rsfis/RIAN-MICROCOMPUTER/cart/aliexpress.png

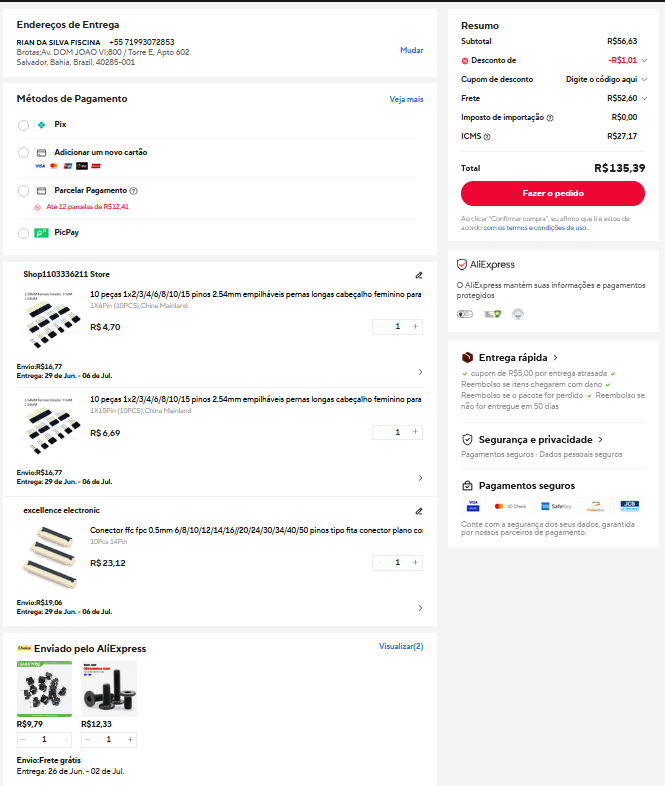
cart/aliexpress.png
