rsfis/RIAN-MICROCOMPUTER/cart/jlc.png

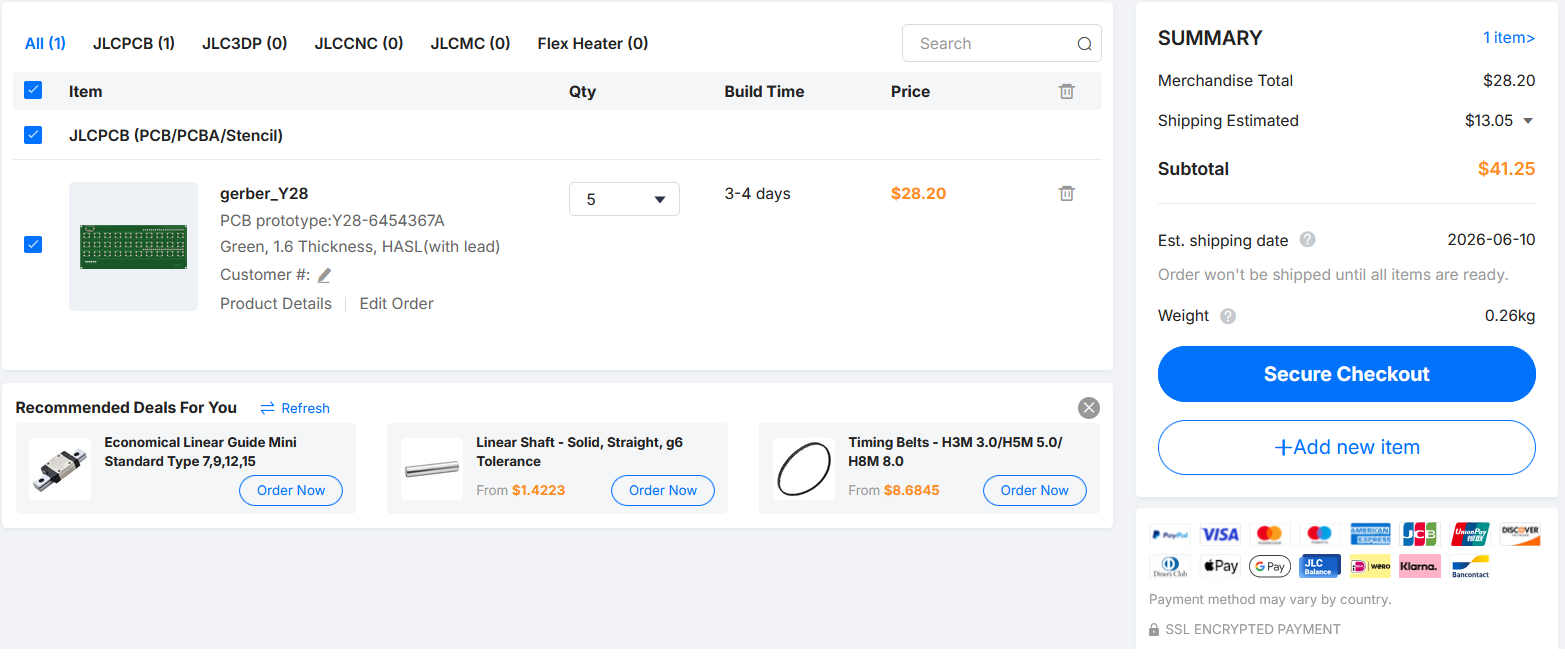
cart/jlc.png
