rsfis/RIAN-MICROCOMPUTER/firmware/!draft/colours.png

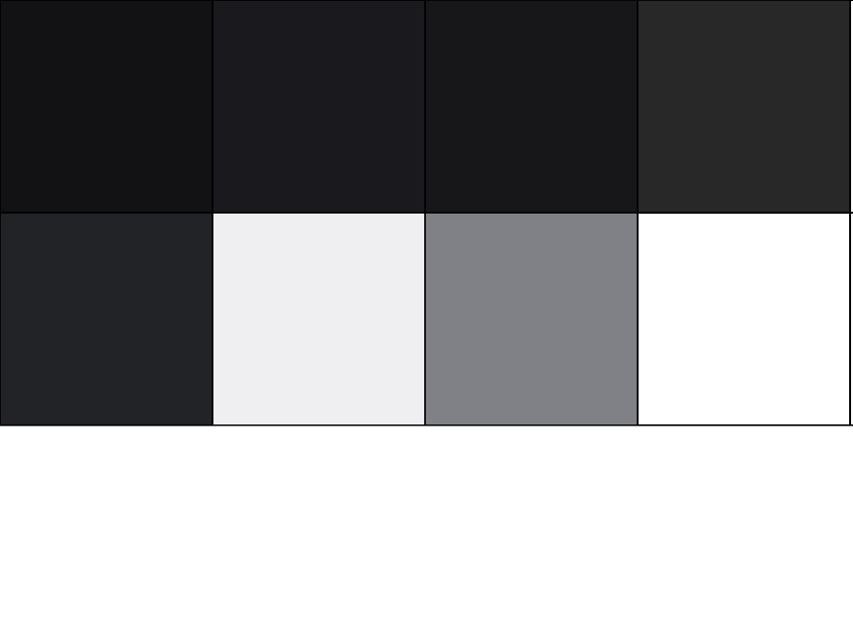
firmware/!draft/colours.png
