rsfis/RIAN-MICROCOMPUTER/firmware/!draft/export/desktop_page.png

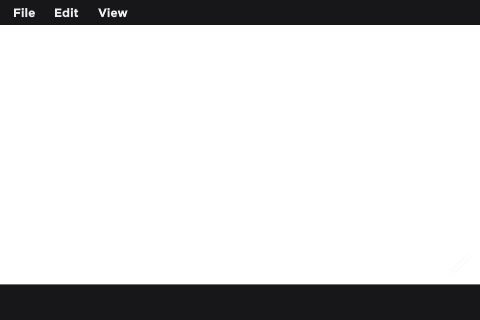
firmware/!draft/export/desktop_page.png
