rsfis/RIAN-MICROCOMPUTER/firmware/!draft/export/initiating_bg.png

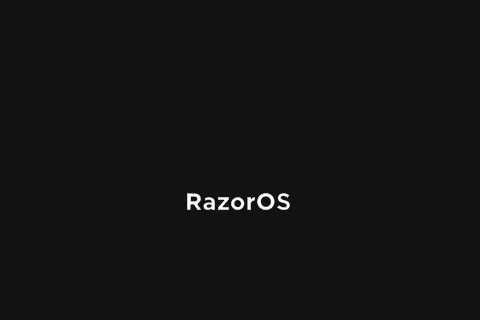
firmware/!draft/export/initiating_bg.png
