rsfis/RIAN-MICROCOMPUTER/firmware/!draft/export/user_login_bg.png

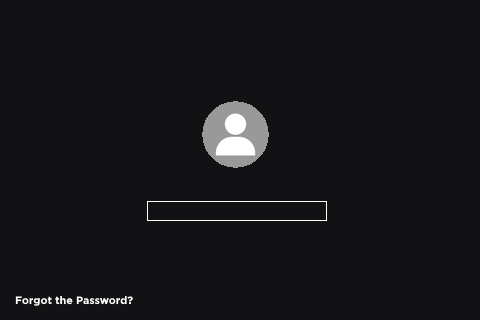
firmware/!draft/export/user_login_bg.png
