rsfis/RIAN-MICROCOMPUTER/reciepts/ali-femaleheaders-reciept.png

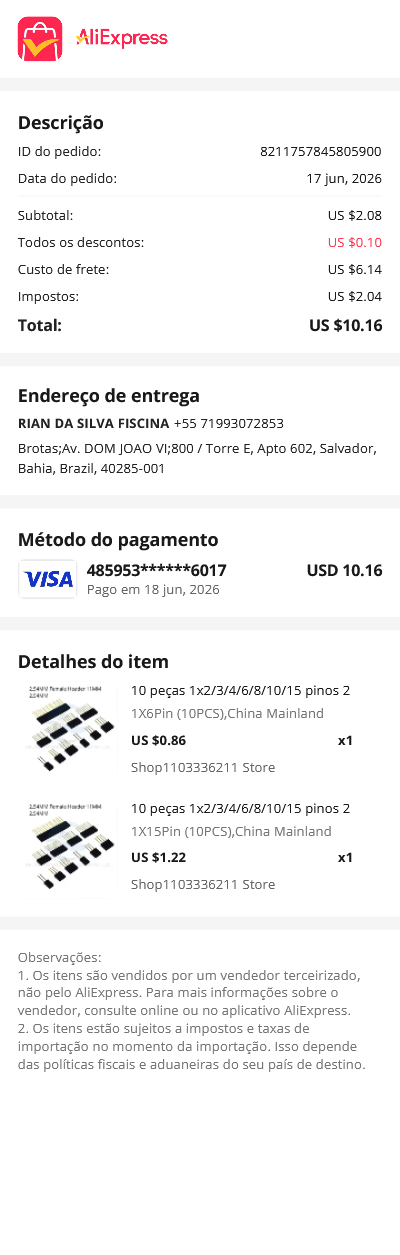
reciepts/ali-femaleheaders-reciept.png
