rsfis/RIAN-MICROCOMPUTER/reciepts/ali-flatcablesocket-reciept.png

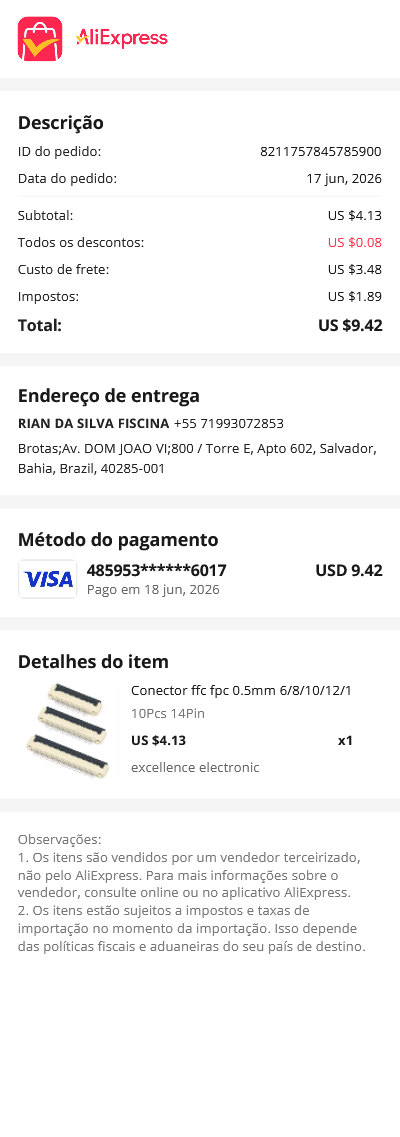
reciepts/ali-flatcablesocket-reciept.png
