rsfis/RIAN-MICROCOMPUTER/reciepts/ali-m3_screws-reciept.png

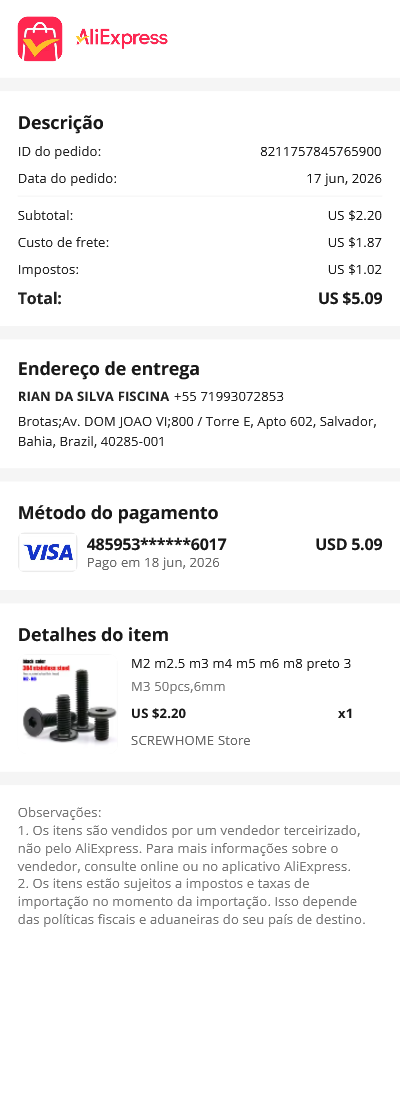
reciepts/ali-m3_screws-reciept.png
