rsfis/RIAN-MICROCOMPUTER/unified pcb/imgs/in2_cu.png

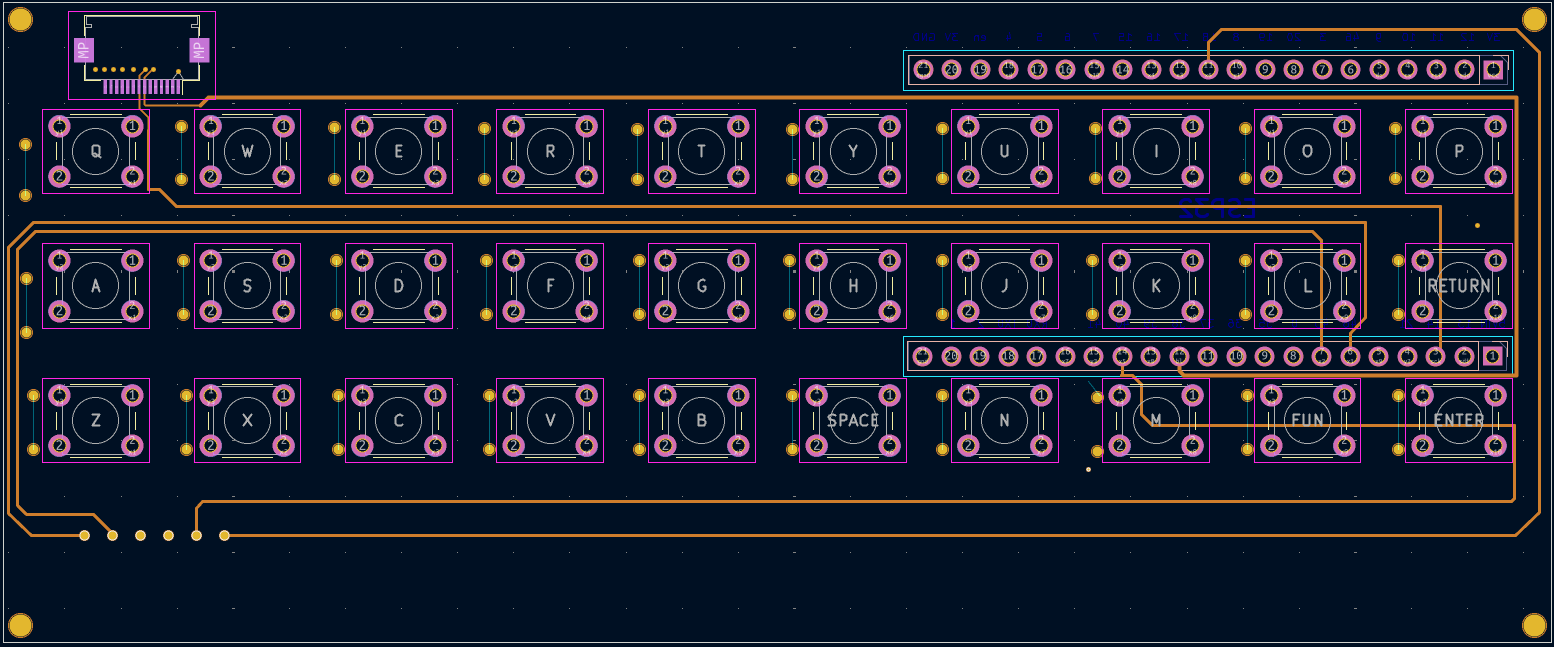
unified pcb/imgs/in2_cu.png
