rsfis/RIAN-MICROCOMPUTER/reciepts/mercadolivre-soldering-reciept.png

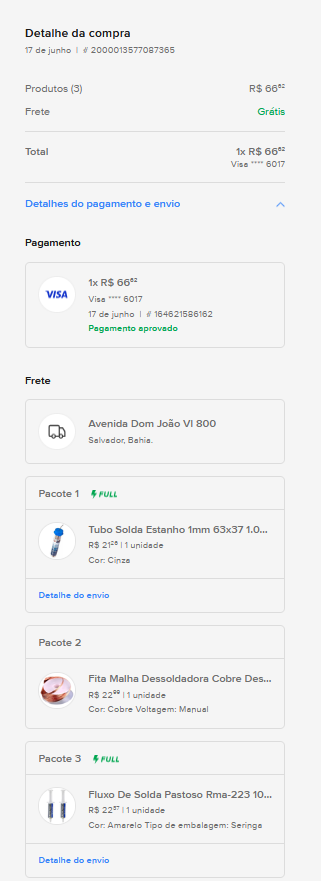
reciepts/mercadolivre-soldering-reciept.png
