rsfis/RIAN-MICROCOMPUTER/wiring diagram.png

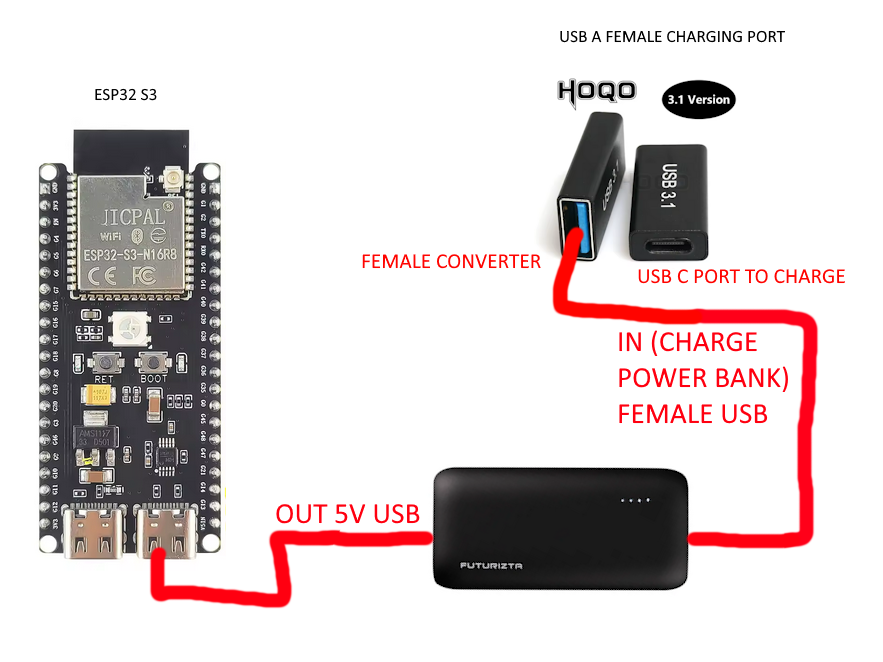
wiring diagram.png
