rsfis/RIAN-MICROCOMPUTER/tests/3d_models/sky.h

#pragma once
#include <vector>
#include <cstdint>

static const float sky_0_vertices[] = {
    -0.234f, 0.978f, -0.244f, -0.234f, 0.978f, -0.244f, 0.004f, 0.134f, -1.031f,
    0.224f, -0.588f, -0.839f, 0.580f, 0.450f, -0.718f, 0.582f, -0.329f, -0.788f,
    0.139f, 1.013f, -0.041f, 0.358f, 0.731f, -0.652f, 0.937f, -0.098f, -0.426f,
    0.760f, -0.641f, -0.220f, 0.295f, -0.950f, -0.232f, 0.903f, 0.512f, -0.003f,
    1.029f, -0.074f, 0.147f, 0.597f, 0.833f, 0.103f, 0.718f, 0.483f, 0.555f,
    0.578f, -0.339f, 0.808f, 0.363f, 0.299f, 0.923f, 0.556f, -0.726f, 0.511f,
    0.321f, -0.966f, 0.137f, 0.184f, 0.870f, 0.503f, -0.245f, 0.521f, 0.861f,
    -0.088f, -0.139f, 1.016f, -0.259f, -0.791f, 0.630f, -0.659f, -0.104f, 0.787f,
    -0.698f, 0.550f, 0.500f, -0.412f, 0.859f, 0.400f, -0.989f, 0.258f, 0.215f,
    -0.989f, 0.258f, 0.215f, -0.881f, -0.496f, 0.259f, -0.881f, -0.496f, 0.259f,
    -0.859f, -0.209f, -0.571f, -0.746f, -0.662f, -0.189f, -0.746f, -0.662f, -0.189f,
    -0.751f, 0.658f, -0.268f, -0.751f, 0.658f, -0.268f, -0.300f, -0.984f, -0.024f,
    -0.300f, -0.984f, -0.024f, -0.300f, -0.984f, -0.024f, -0.483f, 0.428f, -0.828f,
    -0.267f, -0.491f, -0.863f, -0.268f, -0.864f, -0.474f
};

static const unsigned int sky_0_indices[] = {
    40, 10, 37, 7, 4, 2, 2, 5, 3,
    5, 4, 8, 5, 9, 3, 4, 7, 11,
    6, 13, 7, 10, 9, 18, 8, 11, 12,
    9, 12, 17, 36, 10, 18, 12, 14, 15,
    6, 19, 13, 13, 19, 14, 14, 19, 16,
    16, 21, 15, 16, 20, 21, 15, 21, 22,
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
    93, 121, 160, 255, 86, 113, 153, 255, 77,
    102, 143, 255, 78, 104, 145, 255, 86, 115,
    156, 255, 82, 113, 154, 255, 70, 102, 141,
    255, 70, 99, 139, 255, 88, 118, 157, 255,
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
};

static const int sky_0_texWidth = 200;
static const int sky_0_texHeight = 112;
