rsfis/RIAN-MICROCOMPUTER/tests/text/Geometos.h

// Created by ttf2gfx utility
const uint8_t Geometos14ptBitmaps[] PROGMEM = {
    // Bitmap Data:
    0x00                                                                       // ' '
   ,0xFF,0xFF,0xFF,0xFF,0xFF,0xEE,0x66,0x00,0xFF,0xFF                          // '!'
   ,0xF3,0xFC,0xEF,0x3B,0xCE,0x73,0x98,0xE0                                    // '"'
   ,0x00,0x3C,0x78,0x00,0xF1,0xE0,0x01,0xE3,0xC0,0x03,0x87,0x00,0x0F,0x1E,0x01
   ,0xFF,0xFF,0xC3,0xFF,0xFF,0x07,0xFF,0xFE,0x1F,0xFF,0xF8,0x07,0x87,0x00,0x0E
   ,0x1E,0x01,0xFF,0xFF,0x87,0xFF,0xFE,0x0F,0xFF,0xFC,0x1F,0xFF,0xF8,0x47,0x8F
   ,0x00,0x1E,0x1C,0x00,0x3C,0x78,0x00,0x70,0xF0,0x01,0xE3,0xC0,0x00           // '#'
   ,0x03,0xC0,0x03,0xC0,0x0F,0xE0,0x3F,0xF8,0x7F,0xFE,0xFF,0xFF,0xF8,0x1E,0xF0
   ,0x04,0xF0,0x00,0xF8,0x00,0x7F,0x80,0x3F,0xF8,0x0F,0xFC,0x00,0x7E,0x00,0x1F
   ,0x40,0x0F,0x30,0x0F,0x7C,0x1F,0xFF,0xFF,0x3F,0xFE,0x1F,0xFC,0x03,0xF0,0x03
   ,0xC0,0x03,0xC0                                                             // '$'
   ,0x1E,0x00,0xF0,0x7F,0x80,0xE0,0x7F,0x81,0xC0,0xF3,0xC3,0xC0,0xF3,0xC3,0x80
   ,0xF3,0xC7,0x00,0xF3,0xC7,0x00,0xF3,0xCE,0x00,0x7F,0x9E,0x00,0x7F,0x1C,0xF8
   ,0x1E,0x39,0xFC,0x00,0x3B,0xFE,0x00,0x77,0xDF,0x00,0xF7,0x8F,0x00,0xE7,0x8F
   ,0x01,0xC7,0x8F,0x01,0xC7,0xDF,0x03,0x83,0xFE,0x07,0x81,0xFC,0x07,0x00,0xF8 // '%'
   ,0x00,0x00,0x07,0xE0,0x07,0xF8,0x03,0xFE,0x03,0xC7,0x01,0xE3,0x80,0xF1,0xC0
   ,0x79,0xE0,0x1F,0xF0,0x0F,0xF0,0x07,0xE1,0x07,0xF9,0xE7,0xBE,0xF7,0x8F,0xF3
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
	  {  1104,  15,  20,  19,    2,  -20 }, // 'E
	  {  1142,  15,  20,  19,    2,  -20 }, // 'F
	  {  1180,  21,  20,  23,    1,  -20 }, // 'G
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
};
const GFXfont Geometos14pt PROGMEM = {
    (uint8_t  *)Geometos14ptBitmaps,
    (GFXglyph *)Geometos14ptGlyphs,
    0x20, 
    0xFF, 
    28
};
